ChiragKotian/Motor-Controller-for-cobots/motorcontoller/controller/3-phase-bridge-and-BLDC-motor.jpg

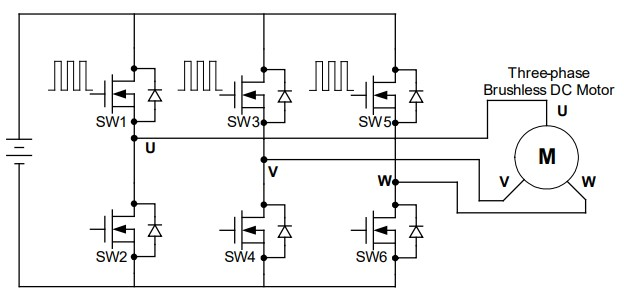
motorcontoller/controller/3-phase-bridge-and-BLDC-motor.jpg
