ChiragKotian/Motor-Controller-for-cobots/motorcontoller/controller/7_4.jpeg

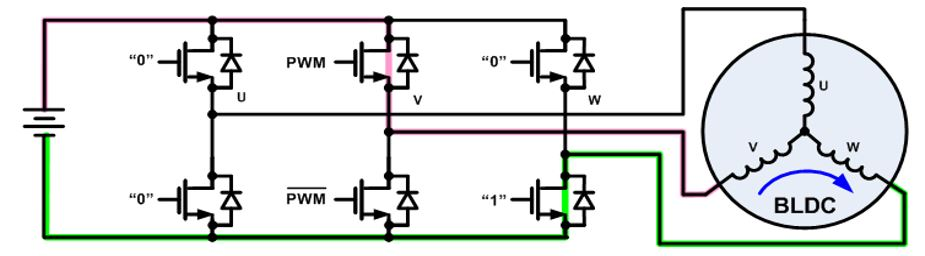
motorcontoller/controller/7_4.jpeg
