ChiragKotian/Motor-Controller-for-cobots/motorcontoller/controller/18823-d1969b53b2aad65e50da1c505c1d37b6.jpg

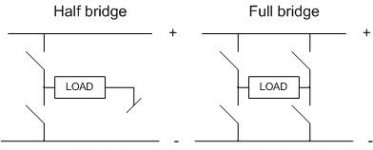
motorcontoller/controller/18823-d1969b53b2aad65e50da1c505c1d37b6.jpg
