ChiragKotian/Motor-Controller-for-cobots/motorcontoller/controller/image-10.png

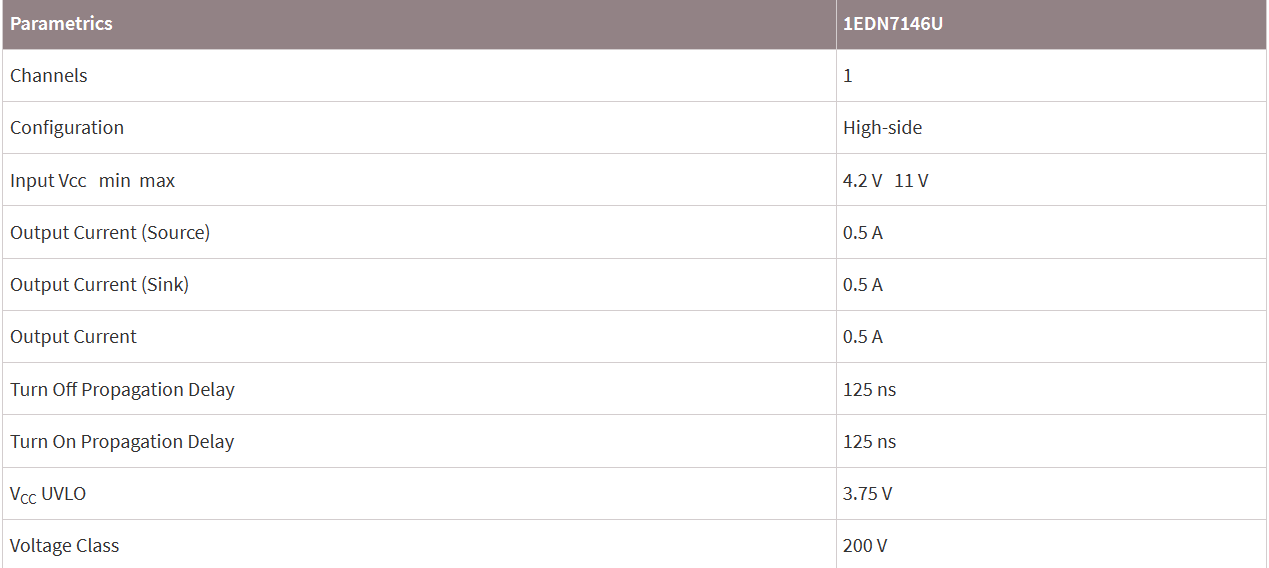
motorcontoller/controller/image-10.png
