ChiragKotian/Motor-Controller-for-cobots/motorcontoller/controller/image-38.png

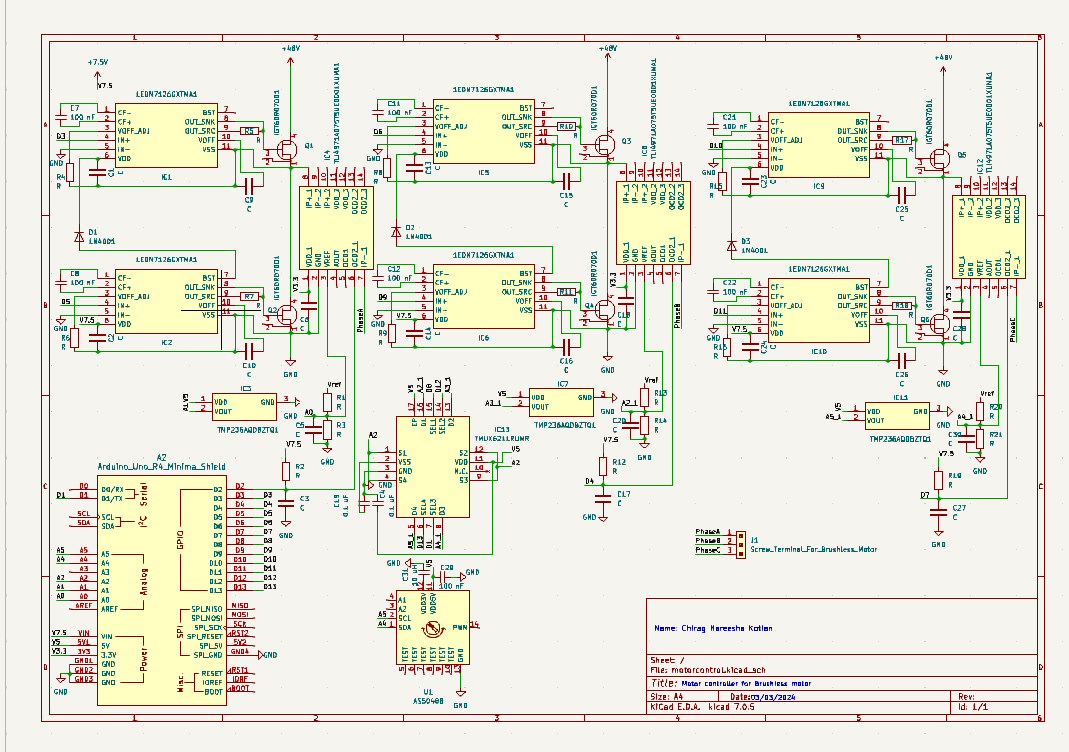
motorcontoller/controller/image-38.png
