ChiragKotian/Motor-Controller-for-cobots/motorcontoller/illustratons/Block diagram of the system.png

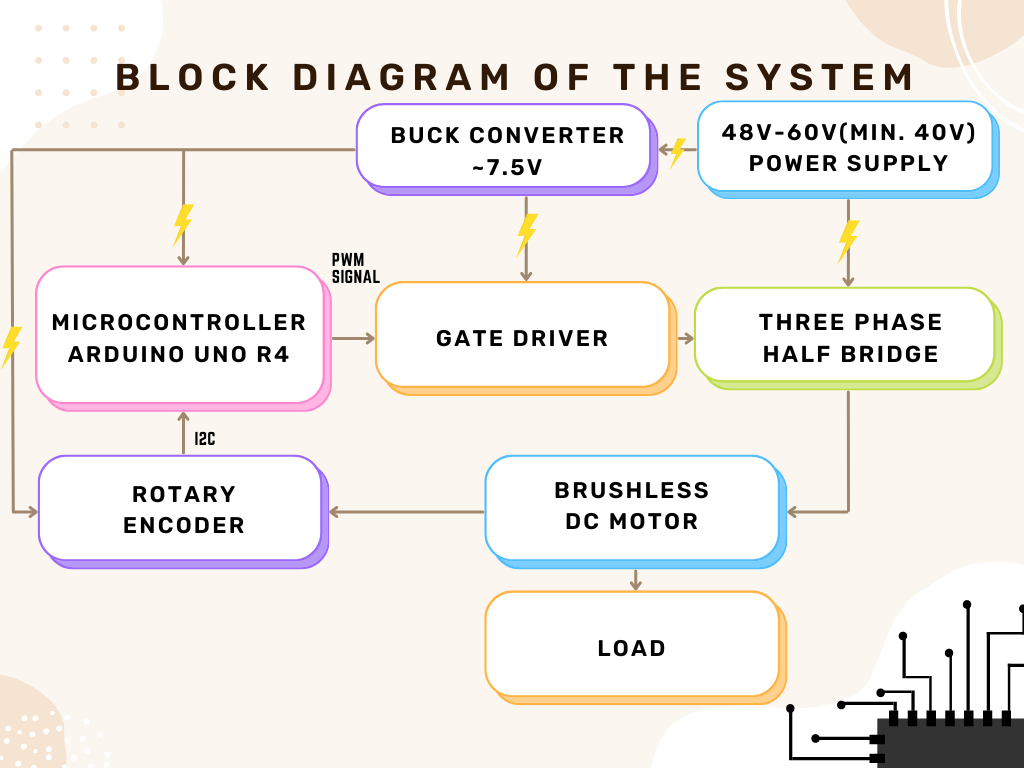
motorcontoller/illustratons/Block diagram of the system.png
