ChiragKotian/Motor-Controller-for-cobots/motorcontoller/motor/Screenshot 2024-02-25 231527.png

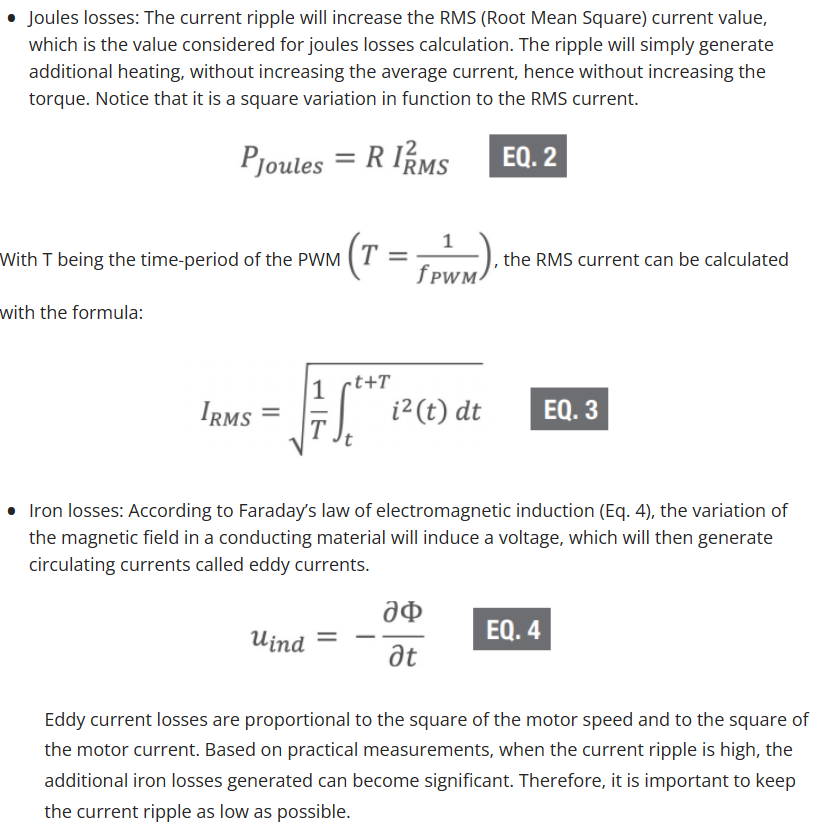
motorcontoller/motor/Screenshot 2024-02-25 231527.png
