ChiragKotian/Motor-Controller-for-cobots/motorcontoller/motor/Turnigy Aerodrive SK3 - 4240-740kv.JPG

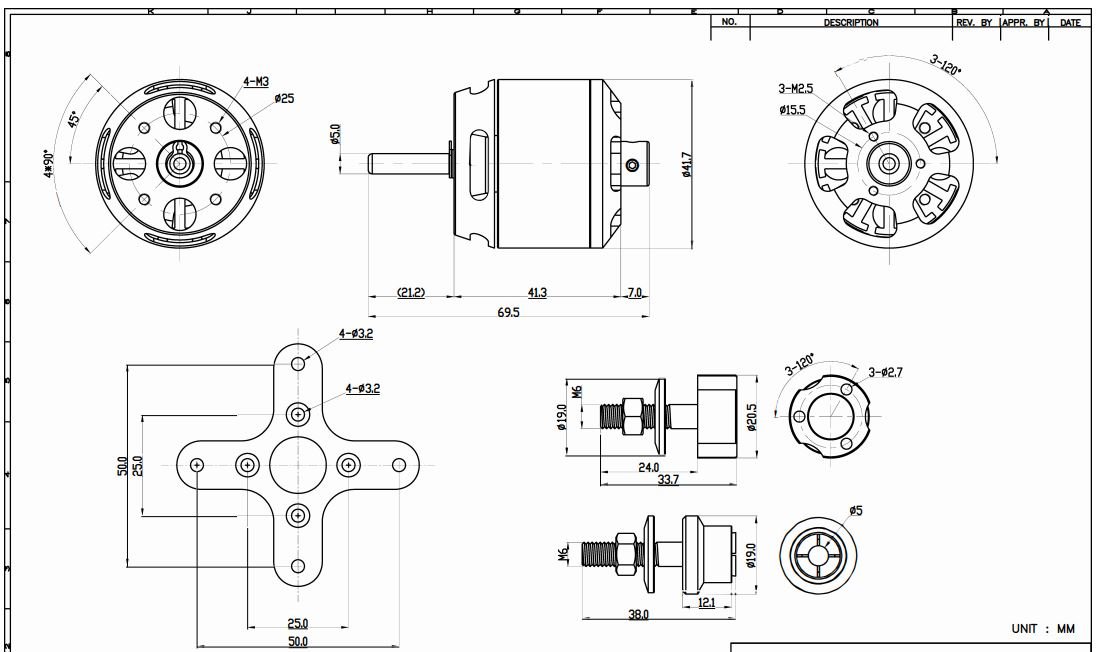
motorcontoller/motor/Turnigy Aerodrive SK3 - 4240-740kv.JPG
